Nicolboy/KICAD-C2000-float-flyback/simulation/results/envelope_18w9_sync.csv

label | vin | vout_target | d | rload | vout_avg | iout_avg | pout_avg | pin_avg | eta_pct | mode | ploss_q1 | ploss_rect | ploss_d1 | ploss_dcr1 | ploss_dcr2 | ploss_rshunt | ploss_cout | ploss_sum | ploss_total_pin_pout | vds_q1_max | vds_q2_max | ipk_pri | irms_pri | il2_end_of_period
11V_6V3 | 11.0 | 6.3 | 0.4006 | 2.1 | 6.8028 | 3.2394 | 22.0374 | 24.1774 | 91.15 | CCM | 1.0896 | 0.3175 | 0.9134 | 0.188 | 0.2734 | 0.0931 | 0.025 | 2.9 | 2.1401 | 54.851 | 63.209 | 7.0749 | 3.5398 | 4.4594
11V_12V6 | 11.0 | 12.6 | 0.5502 | 8.4 | 13.0949 | 1.5589 | 20.414 | 21.6708 | 94.2 | CCM | 0.5892 | 0.1961 | 0.454 | 0.1182 | 0.0954 | 0.0589 | 0.0127 | 1.5245 | 1.2569 | 52.301 | 86.296 | 5.2968 | 2.8073 | 2.0108
20V_6V3 | 20.0 | 6.3 | 0.2602 | 2.1 | 6.7282 | 3.2039 | 21.5563 | 23.4712 | 91.84 | CCM | 1.06 | 0.3145 | 0.9037 | 0.0876 | 0.2245 | 0.0432 | 0.0152 | 2.6486 | 1.9149 | 54.449 | 100.636 | 6.7422 | 2.4168 | 3.1586
20V_12V6 | 20.0 | 12.6 | 0.4006 | 8.4 | 13.3061 | 1.5841 | 21.0778 | 22.2362 | 94.79 | CCM | 0.5284 | 0.2301 | 0.3643 | 0.061 | 0.0844 | 0.0305 | 0.0101 | 1.3088 | 1.1585 | 51.723 | 106.733 | 5.1277 | 2.0166 | 0.7608
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
