Nicolboy/KICAD-C2000-float-flyback/simulation/results/envelope_schottky.csv

label | vin | vout_target | d | rload | vout_avg | iout_avg | pout_avg | pin_avg | eta_pct | mode | ploss_q1 | ploss_rect | ploss_d1 | ploss_dcr1 | ploss_dcr2 | ploss_rshunt | ploss_cout | ploss_sum | ploss_total_pin_pout | vds_q1_max | vds_q2_max | ipk_pri | irms_pri | il2_end_of_period
11V_6V | 11.0 | 6.0 | 0.3828 | 3.6 | 6.1373 | 1.7048 | 10.4631 | 11.8953 | 87.96 | CCM | 0.4204 | 0.7838 | 0.3355 | 0.0497 | 0.0764 | 0.0246 | 0.0071 | 1.6974 | 1.4322 | 51.721 | 19.507 | 3.8411 | 1.8208 | 1.7812
11V_12V | 11.0 | 12.0 | 0.5359 | 14.4 | 12.1161 | 0.8414 | 10.1945 | 11.1398 | 91.51 | CCM | 0.4204 | 0.3773 | 0.3274 | 0.0356 | 0.0293 | 0.0177 | 0.004 | 1.2119 | 0.9453 | 51.355 | 33.618 | 3.3293 | 1.5414 | 0.4373
20V_6V | 20.0 | 6.0 | 0.25 | 3.6 | 6.1187 | 1.6996 | 10.3995 | 11.8868 | 87.49 | CCM | 0.5619 | 0.7693 | 0.4593 | 0.0237 | 0.0648 | 0.0117 | 0.0046 | 1.8954 | 1.4873 | 51.83 | 37.787 | 3.5597 | 1.2582 | 1.1144
20V_12V | 20.0 | 12.0 | 0.3016 | 14.4 | 10.8358 | 0.7525 | 8.1538 | 8.9362 | 91.24 | DCM | 0.4527 | 0.3294 | 0.4059 | 0.0141 | 0.0222 | 0.007 | 0.003 | 1.2342 | 0.7824 | 51.215 | 32.163 | 2.9506 | 0.968 | -0.0
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
