Nicolboy/KICAD-C2000-float-flyback/simulation/results/test_ipd_10w.asc

Cin: cap; 470u
Cout1: cap; 330u ic=6.3
Cout2: cap; 330u ic=6.3
D1: diode; DCLAMP_SMCJ43A
D2sec: diode; DCLAMP_SEC
L1: ind; 10u ic=0
L2: ind; 10u ic=0
Lmesh_pri: ind; 1e-12
Lmesh_sec: ind; 1e-12
M1: nmos; IPD050N10N5
M2: nmos; IPD050N10N5
Rcin_esr: res; 10m
Rcout1_esr: res; 6.5m
Rcout2_esr: res; 6.5m
Rdcr1: res; 15m
Rdcr2: res; 15m
Rload: res; 3.9690
Rshunt: res; 7.5m
V1: voltage; 20.0
Vg1: voltage; PULSE(0 10 0 2n 2n 1.1953u 5.0000u)
Vg2: voltage; PULSE(0 10 1.2953u 2n 2n 3.6047u 5.0000u)
Named nets: vin, 0, n_cin_r, n_pri1, n_pri1b, n_pri2, g1, n_q1s, n_sec1, vout, n_sec1b, n_sec2, g2, n_cout1_r, n_cout2_r
Point point : Vin=20.0V Vout_cible=6.3V Pout_cible=10.0W D=0.2391 200kHz -- masse commune (pas de HV_BIAS), redressement passif (diode de corps Q2, gate=0V)
.lib "C:/Users/Nicolas/workspace_ccstheia/alim-flyback-filament/simulation/models/IPD050N10N5.lib"
.model DCLAMP_SMCJ43A D(BV=47.8 IBV=1m RS=1.0)
.model DCLAMP_SEC D(BV=60 IBV=1m RS=1.0)
K1 L1 L2 0.99
.tran 0 20000.00u 19500.00u 10n uic
.meas TRAN Vout_avg AVG V(vout) FROM 19500.00u TO 20000.00u
.meas TRAN Iout_avg AVG I(Rload) FROM 19500.00u TO 20000.00u
.meas TRAN Pout_avg AVG (V(vout)*I(Rload)) FROM 19500.00u TO 20000.00u
.meas TRAN Pin_avg AVG (-V(vin)*I(V1)) FROM 19500.00u TO 20000.00u
.meas TRAN Ploss_Q1 AVG (I(Lmesh_pri)*(V(n_pri2)-V(n_q1s))) FROM 19500.00u TO 20000.00u
.meas TRAN Ploss_Rect AVG (I(Lmesh_sec)*V(n_sec2)) FROM 19500.00u TO 20000.00u
.meas TRAN Ploss_DCR1 AVG (I(Rdcr1)*I(Rdcr1)*0.015) FROM 19500.00u TO 20000.00u
.meas TRAN Ploss_DCR2 AVG (I(Rdcr2)*I(Rdcr2)*0.015) FROM 19500.00u TO 20000.00u
.meas TRAN Ploss_Rshunt AVG (I(Rshunt)*I(Rshunt)*0.0075) FROM 19500.00u TO 20000.00u
.meas TRAN Ploss_D1 AVG (-I(D1)*V(n_pri2)) FROM 19500.00u TO 20000.00u
.meas TRAN Ploss_D2sec AVG (-I(D2sec)*V(n_sec2)) FROM 19500.00u TO 20000.00u
.meas TRAN Ploss_Cout AVG (I(Rcout1_esr)*I(Rcout1_esr)*0.0065+I(Rcout2_esr)*I(Rcout2_esr)*0.0065) FROM 19500.00u TO 20000.00u
.meas TRAN Vds_Q1_max MAX (V(n_pri2)-V(n_q1s)) FROM 19500.00u TO 20000.00u
.meas TRAN Vds_Q2_max MAX V(n_sec2) FROM 19500.00u TO 20000.00u
.meas TRAN Ipk_pri MAX I(L1) FROM 19500.00u TO 20000.00u
.meas TRAN Irms_pri RMS I(L1) FROM 19500.00u TO 20000.00u
.meas TRAN IL2_end_of_period FIND I(L2) AT 19999.9500u
